MASSIMUS3D/Esmeril/Fotos Programação em bloco/1.PNG

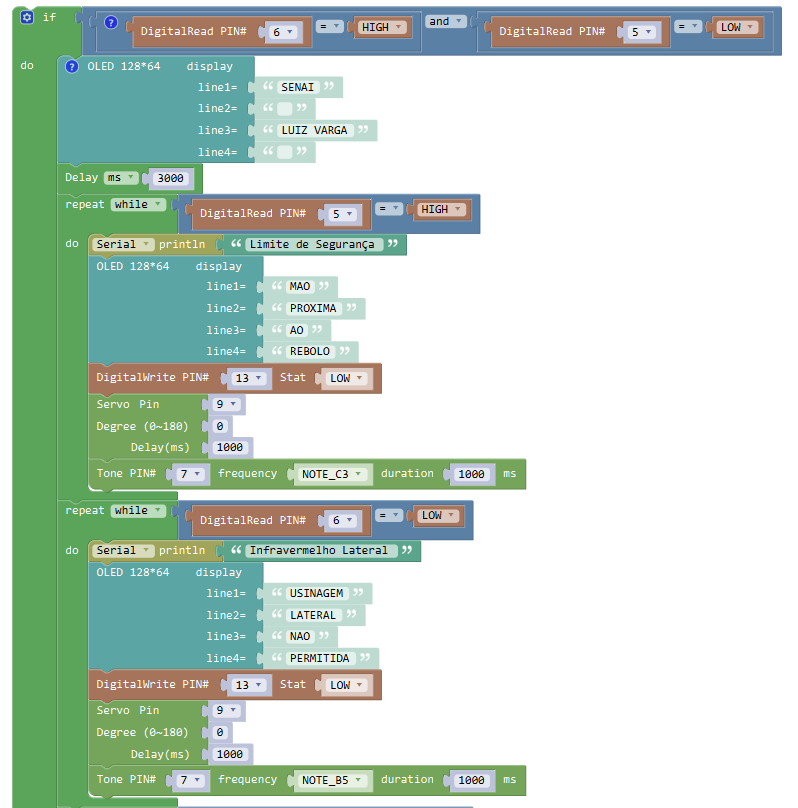
Fotos Programação em bloco/1.PNG
