MASSIMUS3D/Esmeril/Fotos Programação em bloco/2.PNG

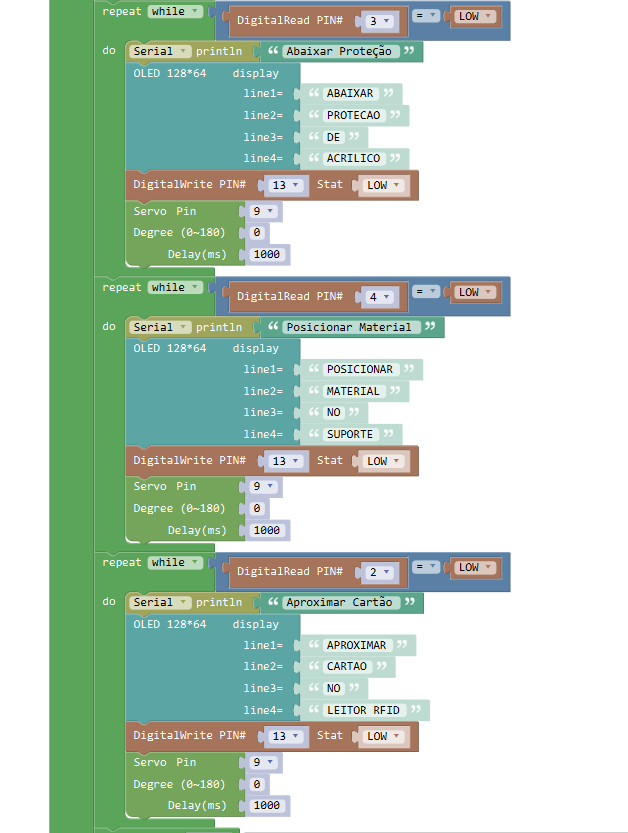
Fotos Programação em bloco/2.PNG
