MASSIMUS3D/Esmeril/Fotos Programação em bloco/3.PNG

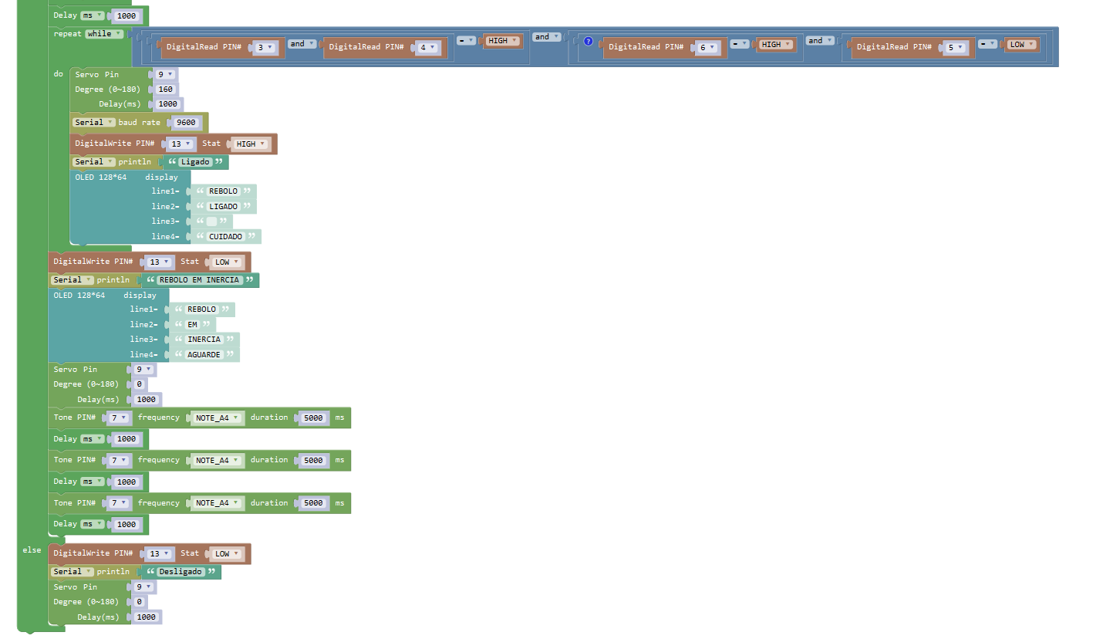
Fotos Programação em bloco/3.PNG
